PatternAgents/SitV/SitV/images/osh_board1.png

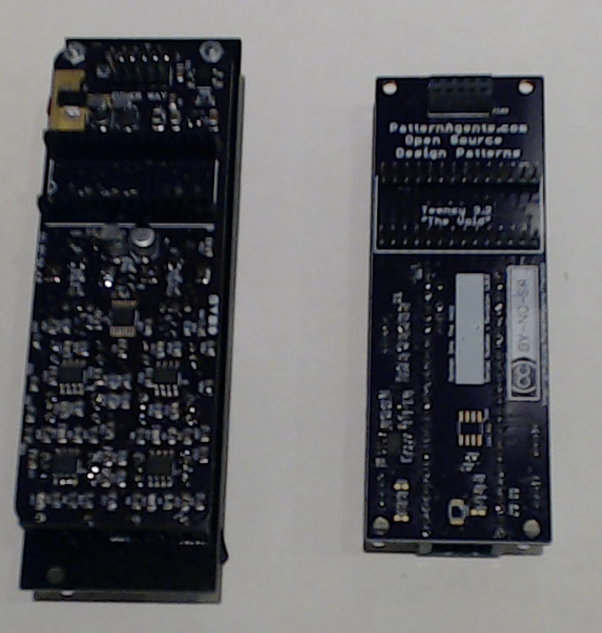
SitV/images/osh_board1.png
