PatternAgents/SitV/SitV/images/osh_board2.png

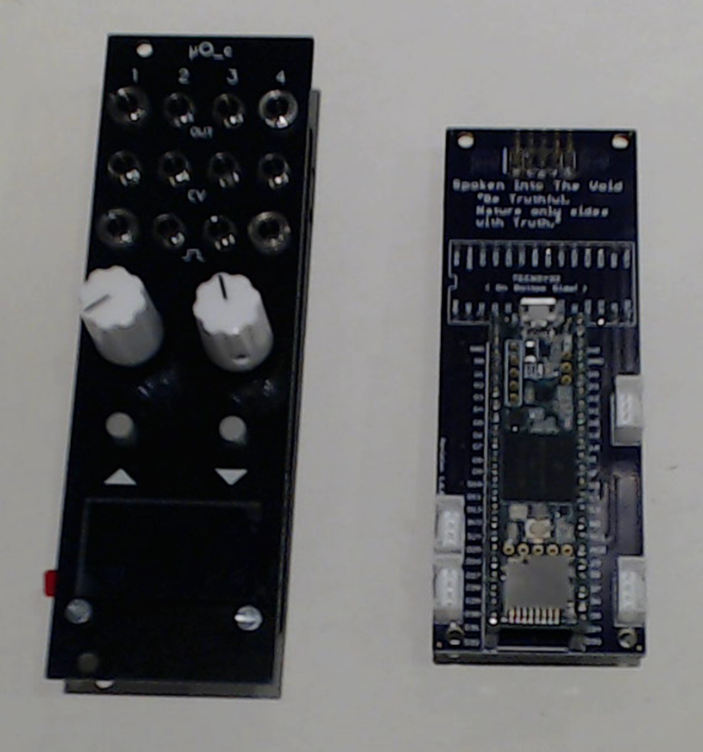
SitV/images/osh_board2.png
