PatternAgents/SitV/SitV/images/osh_board3.png

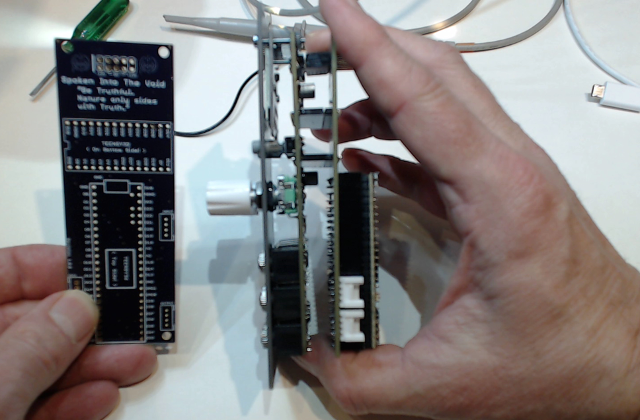
SitV/images/osh_board3.png
