PatternAgents/SitV/SitV/images/osh_board4.png

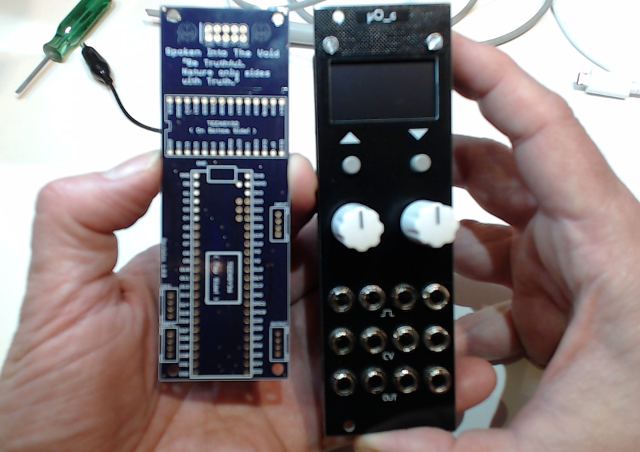
SitV/images/osh_board4.png
