PatternAgents/SitV/SitV/images/uO_C.jpg

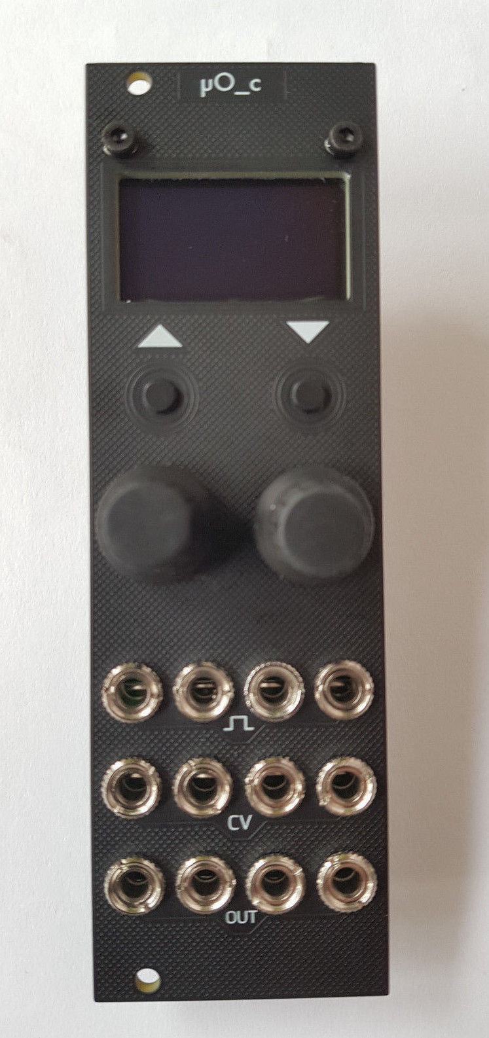
SitV/images/uO_C.jpg
