PatternAgents/SitV/SitV/images/uO_C_osh_top.png

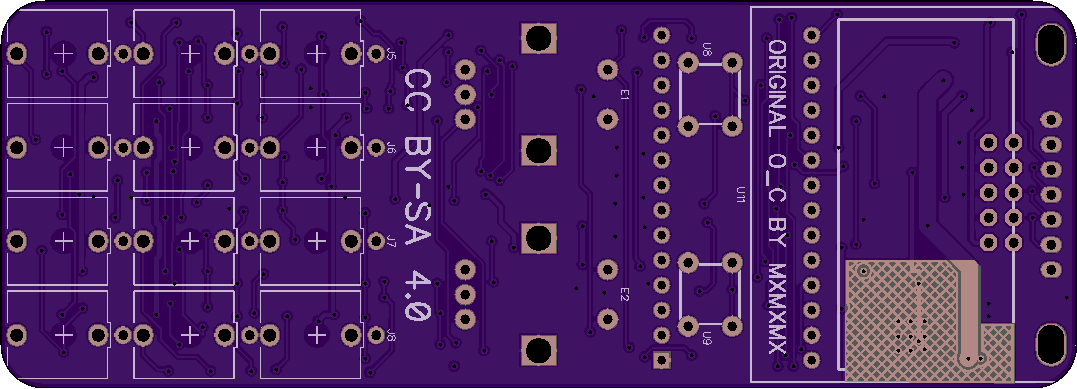
SitV/images/uO_C_osh_top.png
