PatternAgents/SitV/SitV/software/rsvp_sitv/rsvp_sitv/EEPROM.ino

/*  Embedis - Embedded Dictionary Server
    Copyright (C) 2015, 2016, 2017, 2018 PatternAgents, LLC

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
    You should have received a copy of the GNU General Public License
    along with this program.  If not, see <http://www.gnu.org/licenses/>.
*/

// Add an "EEPROM" dictionary to Embedis, using the Ardunio EEPROM API
//
// We show in this example how to use Embedis to hold configuration settings in EEPROM.
// Due to Wear leveling issues this is not recommended for real-time and changing data.
// Use SRAM, NVSRAM, FRAM or other suitable storage technology for rapidly changing data sets!
//
// To configure an EEPROM dictionary, call EEPROM_setup from your
// main setup() function. Optionally, supply the database name you want to use.
// e.g. EEPROM_setup();
//      EEPROM_setup( F("MYEEPROM") );
//
// Use the Embedis "select" command to enable your optional database name
// e.g. embedis-> select MYEEPROM
// The Embedis default database is "EEPROM", using the internal EEPROM memory.
// (or in the case of ESP8266 or Arduino Due, Emulated EEPROM...)
//
#include <EEPROM.h>

// Set your particular EEPROM size, which may want to be less than the physical device size.
// As an example, a 16K byte EEPROM might use only the first 4096 bytes to
// hold an IMPI, DeviceTree or other persistant data structure. 
// Since Embedis writes from high memory to low memory, you could use 12K bytes
// of that memory for an Embedis Keystore, coexisting with the other persistant data structure.
// If E2END isn't defined you can uncoment the line below and manually set the size (in bytes).
//
//#define E2END 1023
const size_t EEPROM_SIZE = E2END + 1;

void EEPROM_setup() 
{
    EEPROM_setup( F("EEPROM") );
}

void EEPROM_setup(const String& dict) 
{
    Embedis::dictionary( dict,
        EEPROM_SIZE,
        [](size_t pos) -> char { return EEPROM.read(pos); },
        [](size_t pos, char value) { EEPROM.write(pos, value); }
    );
}
