PatternAgents/SitV/SitV/software/rsvp_sitv/rsvp_sitv/rsvp.h

#ifndef RSVP_H_
#define RSVP_H_

	#include <Audio.h>
	#include <Wire.h>
	#include <SPI.h>
	#include <SD.h>
	#include <SerialFlash.h>
	#include <EEPROM.h>
	#include <Embedis.h>

	#include "rsvp_options.h"
	#include "rsvp_pins.h"
  #include "src/samples/piano_samples.h"

#endif
