PatternAgents/SitV/SitV/software/o_c_V1_3_3_sitv/OC_options.h

/*
 *
 * compile options.
 *
 */

#ifndef OC_OPTIONS_H_
#define OC_OPTIONS_H_

/* ------------ uncomment for Buchla/non-octaval/quartertone support: -------------------------------  */
//#define BUCHLA_SUPPORT
/* ------------ uncomment for use with Northernlight 4U version: ------------------------------------  */
//#define BUCHLA_4U
/* ------------ uncomment for boring app names ------------------------------------------------------  */
//#define BORING_APP_NAMES
/* ------------ print debug messages to USB serial --------------------------------------------------  */
//#define PRINT_DEBUG
/* ------------ flip screen / IO mapping ------------------------------------------------------------  */
//#define FLIP_180
/* ------------- The Void/Quad Varient Defines --------------------------------------------------------*/
#define THEVOID_QT
#endif
