PatternAgents/SitV/SitV/software/tests/Embedis_test/Embedis_test.ino

/*  Embedis - Embedded Dictionary Server
    Copyright (C) 2015 PatternAgents, LLC

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
    You should have received a copy of the GNU General Public License
    along with this program.  If not, see <http://www.gnu.org/licenses/>.
*/
/*
   ====================================================================================== 

    Embedis_I2C_FRAM : Embedis example with EEPROM and I2C FRAM Keystores
    ---------------------------------------------------------------------
    This example Arduino IDE sketch works on a number of platforms including AVR & ESP8266
    and provides an Embedis server that store permenant (persistant) data in
    either the internal EEPROM of the processor or an external I2C FRAM,
    or Ferro-Electric Random Access Memory, such as the MB85RC256V or FM24V10 type parts.

    The Embedis server can be used to get/set keys in the EEPROM or FRAM databases,
    and can be used to store project and configuration settings. 
    You no longer need to embed  that "data" into your "program"! 
    The EEPROM & FRAM are persistant memory structures, and can be
    used across multiple projects to configure your program setting for
    the specific hardware and network configuration you are using. 
    
    Now, you don't need to recompile your program and reflash your device
    in order to change the device settings anymore.

    We think that this is a much better mechanism for storing settings between projects.
    Once you start using Embedis for your projects, you'll see how quick and easy
    it is to move and reconfigure your devices without needing to recompile 
    and reflash your device firmware just to change a configuration setting.
    Now settings can be changed "on-the-fly" with just an Embedis Server.
    (some settings changes however, will require a restart/reboot to take effect.)

   ======================================================================================
*/

#include <Embedis.h>
#include <EEPROM.h>

// Embedis will run on the Serial port. Use the Arduino
// serial monitor and send "COMMANDS" to get started.
// Make sure "No line ending" is -not- selected. All others work.
//
Embedis embedis(Serial);

void setup() 
{
    Serial.begin(115200);
    while (!Serial) {
      ; // wait for serial port to connect. Needed for native USB
    }

    LOG( String() + F(" ") );
    LOG( String() + F("[ Embedis I2C_FRAM Sketch ]") );
    
    setup_EEPROM();
    setup_I2C_FRAM();
    setup_commands();

    LOG( String() + F("[ type 'commands' to get a list... ]") );    
}

void loop() 
{
    /* Always call the process method fro the main loop to run the Embedis system */
    embedis.process();

    /* Give the internal RTOS time to task switch in ESP8266, Edison, Currie, etc.   */
    /* not really necessary on AVR or Cortex platforms, but hey - it doesn't hurt... */
    delay(20); 
}

// This will log to an embedis channel called "log".
// Use SUBSCRIBE LOG to get these messages.
// Logs are also printed to Serial until an empty message is received.
void LOG(const String& message) {
    static bool inSetup = true;
    if (inSetup) {
        if (!message.length()) {
            inSetup = false;
            return;
        }
        Serial.println(message);
    }
    Embedis::publish("log", message);
}
